rasteri/TAStable/images/image6.png

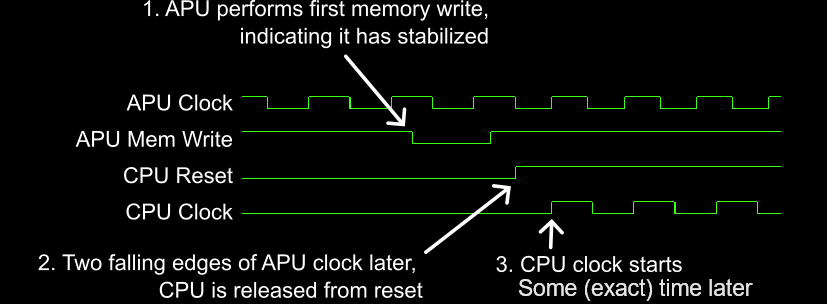
images/image6.png
